sweproj/one-rom/rust/config/json/README.md

# rust/config/json

This directory contains the One ROM PCB hardware configuration files, which tell the software what the port/pin mappings for the various pin types are.

This allows new hardware revisions (i.e. new PCB layouts with different pin mappings) to be supported without needing to modify the source code.

It also contains the [supported chip type hardware configuration file](chip-types.json), which tells One ROM what chips to support and how to support them.

## Usage

See the `*.json` files in this directory for the format of the configuration files.  There are some restrictions on which pins can be used for which pin types:

- All pins of a particular type (address, data, CS/CE/OE in particular) must be on the same port.
- For now, CS/CE/OE pins must share the same port as the address pins, to allow a single STM32F4 port to be read for both address and chip select status.

You should store your files either in:

- [`user/`](/rust/config/json/user/) - for your own, private, hardware configurations
- [`third-party/`](/rust/config/json/third-party/) - for hardware configurations that you plan to submit pull requests for, and want to share with the community

The `onerom-config` crate is generated and built automatically from these config files, and published to crates.io.  This is then used by tools like `sdrr-gen` to generated the One ROM firmware.
