sweproj/one-rom/sdrr-pcb/verified/fire-28-a3/README.md

# One ROM Fire 28 pin 

**Verified - This design only differs from A2 in correcting the SWD CLK/DIO silkscreen labels.

A3 revision of the 28 pin Fire ROM board.  Combined USB/Pro version with USB-C and SWD header pins.

Very minor difference from revision A2:
- CLK/DIO silkscreen labels swapped to correct positions.

## Contents

- [Schematic](./fire-28-a3-schematic.pdf)
- [Fab Files](fab/)
- [KiCad Design Files](kicad/)
- [Errata](#errata)
- [Notes](#notes)
- [Changelog](#changelog)
- [BOM](#bom)

## Errata

## Notes

## Changelog

## BOM

See fab files.
