sweproj/one-rom/sdrr-pcb/verified/fire-28-a2/README.md

# One ROM Fire 28 pin 

A2 revision of the 28 pin Fire ROM board.  Combined USB/Pro version with USB-C and SWD header pins.

Minor differences from revision A:
- Programming pins have been slightly rearranged.

## Contents

- [Schematic](./fire-28-a2-schematic.pdf)
- [Fab Files](fab/)
- [KiCad Design Files](kicad/)
- [Errata](#errata)
- [Notes](#notes)
- [Changelog](#changelog)
- [BOM](#bom)

## Errata

The silkscreen on this revision mislabels the SWD CLK and DIO pins.  The CLK is DIO and DIO is CLK.

## Notes

## Changelog

## BOM

See fab files.
