sweproj/one-rom/sdrr-pcb/verified/fire-28-a/README.md

# One ROM Fire 28 pin 

First revision of the 28 pin Fire ROM board.  Combined USB/Pro version with USB-C and SWD header pins.

## Contents

- [Schematic](./fire-28-a-schematic.pdf)
- [Fab Files](fab/)
- [KiCad Design Files](kicad/)
- [Errata](#errata)
- [Notes](#notes)
- [Changelog](#changelog)
- [BOM](#bom)

## Errata

## Notes

## Changelog

## BOM

See fab files.
