sweproj/one-rom/rust/lab/src/main.rs

//! One ROM Lab firmware

// Copyright (c) 2025 Piers Finlayson <piers@piers.rocks>
//
// MIT licence

#![no_std]
#![no_main]
#![feature(type_alias_impl_trait)]
#![feature(impl_trait_in_assoc_type)]

extern crate alloc;

#[allow(unused_imports)]
use log::{debug, error, info, trace, warn};

use embassy_executor::Spawner;
use embassy_executor::main as embassy_main;
use embassy_stm32::gpio::Flex;
use embassy_stm32::rcc::clocks;

#[cfg(feature = "repeat")]
use embassy_time::Timer;

use embedded_alloc::LlffHeap as Heap;
#[cfg(feature = "usb")]
use panic_probe as _;
#[cfg(not(feature = "usb"))]
use panic_rtt_target as _;

#[cfg(feature = "control")]
mod control;
mod error;
mod info;
mod logs;
mod rcc;
mod rom;
mod types;
#[cfg(feature = "usb")]
mod usb;

pub use error::Error;
pub use rom::{Id as RomId, Rom};

use info::{LAB_RAM_INFO, PKG_VERSION};

#[global_allocator]
static HEAP: Heap = Heap::empty();

#[cortex_m_rt::pre_init]
unsafe fn pre_init() {
    #[cfg(feature = "usb")]
    usb::check_bootloader_flag();
    info::copy_lab_ram_info();
}

#[embassy_main]
async fn main(_spawner: Spawner) {
    // Initialize the heap allocator
    {
        use core::mem::MaybeUninit;
        const HEAP_SIZE: usize = 1024;
        static mut HEAP_MEM: [MaybeUninit<u8>; HEAP_SIZE] = [MaybeUninit::uninit(); HEAP_SIZE];
        unsafe { HEAP.init(&raw mut HEAP_MEM as usize, HEAP_SIZE) }
    }

    // Set up clock config
    let mut config = embassy_stm32::Config::default();
    #[cfg(feature = "usb")]
    rcc::configure_hse_usb(&mut config);
    #[cfg(not(feature = "usb"))]
    rcc::configure_hsi(&mut config);

    // Get peripherals
    let p = embassy_stm32::init(config);

    // Configure clocks
    let clocks = clocks(&p.RCC);

    // Init USB/logging
    #[cfg(feature = "usb")]
    {
        let usb_device = usb::Usb::new(p.USB_OTG_FS, p.PA12, p.PA11);
        usb::run(_spawner, usb_device);
        usb::init_logger();
    }
    #[cfg(not(feature = "usb"))]
    logs::init_rtt();

    info!("-----");
    info!("One ROM Lab v{}", PKG_VERSION);
    info!("Copyright (c) 2025 Piers Finlayson");

    // Log clocks
    info!("-----");
    match clocks.sys.to_hertz() {
        Some(hz) => debug!("SYSCLK: {hz}"),
        None => warn!("SYSCLK: Unknown"),
    }

    debug!(
        "One ROM Lab Flash Info address: {:#010X}",
        &info::LAB_FLASH_INFO as *const _ as usize
    );
    #[allow(static_mut_refs)]
    unsafe {
        debug!(
            "One ROM Lab RAM Info address:   {:#010X}",
            &LAB_RAM_INFO as *const _ as usize
        );
    }

    // Collate the address and data pins
    let addr_pins = [
        Flex::new(p.PC5),
        Flex::new(p.PC4),
        Flex::new(p.PC6),
        Flex::new(p.PC7),
        Flex::new(p.PC3),
        Flex::new(p.PC2),
        Flex::new(p.PC1),
        Flex::new(p.PC0),
        Flex::new(p.PC8),
        Flex::new(p.PC13),
        Flex::new(p.PC11),
        Flex::new(p.PC12),
        Flex::new(p.PC9),
        Flex::new(p.PC10), // 2364 CS pin, set as "A13"
    ];
    let data_pins = [
        Flex::new(p.PA7),
        Flex::new(p.PA6),
        Flex::new(p.PA5),
        Flex::new(p.PA4),
        Flex::new(p.PA3),
        Flex::new(p.PA2),
        Flex::new(p.PA1),
        Flex::new(p.PA0),
    ];

    // Create the ROM object
    let mut rom = Rom::new(addr_pins, data_pins);
    unsafe {
        LAB_RAM_INFO.rom_data = rom.buf.as_ptr() as *const core::ffi::c_void;
    }
    rom.init();

    #[cfg(feature = "control")]
    {
        let mut control = control::Control::new(rom);
        control.run().await;
    }

    #[cfg(feature = "qa")]
    {
        info!("QA mode");
        #[cfg(feature = "usb")]
        info!("Press `d` to enter DFU mode");
        loop {
            #[cfg(not(feature = "usb"))]
            match rom.read_rom().await {
                Some(_) => info!("ROM read successfully"),
                None => info!("Failed to read ROM"),
            }
            #[cfg(feature = "usb")]
            match embassy_time::with_timeout(embassy_time::Duration::from_secs(5), usb::recv_key())
                .await
            {
                Ok(key) => {
                    if key == b'd' {
                        info!("Entering DFU mode...");
                        usb::enter_dfu_mode().await;
                    }
                }
                Err(_) => (),
            }
            #[cfg(not(feature = "usb"))]
            embassy_time::Timer::after_secs(5).await;
            info!("Reading ROM...");
        }
    }

    #[cfg(not(any(feature = "control", feature = "qa")))]
    {
        loop {
            match rom.read_rom().await {
                Some(_) => break,
                None => info!("Failed to read ROM"),
            }

            #[cfg(feature = "oneshot")]
            {
                info!("Done");
                return;
            }
            #[cfg(feature = "repeat")]
            {
                info!("Waiting 5 seconds before reading again");
                Timer::after_secs(5).await;
            }
        }
    }
}

#[cfg(all(feature = "control", feature = "oneshot"))]
compile_error!("Features 'control' and 'oneshot' are mutually exclusive");
